eldendiss/SwitchFw/sim/LM311_Comp.asc

C1: cap; 10p
C2: cap; 10p
Cpar: cap; 3p
D1: diode; 1N5819
D2: diode; 1N5819
R1: res; 10k
R2: res; 100k
R3: res; 3Meg
R4: res; 100k
R5: res; 10k
R6: res; 1Meg
S1: sw; SWGM
U1: LT1711
VEVENT: voltage; PULSE(0 5 500u 1n 1n 2u 10m)
VFLYBACK: voltage; 500
VSUP: voltage; 5
Named nets: +5V, 0, OUT, TUBE, COMP_IN
.include lm311.lib
.model SWGM SW(Ron=500 Roff=1G Vt=2 Vh=0.5)
.tran 0 2m 0 20m
GM tube model (3p capacitance, 2u dead pulse width)
Original comparator
Anode resistor
Cable parasistics
